NanoVHF/Meshtastic-DIY/Antennas/3...8 el PCB Yagi/3el_870MHz_D4mm_3el_basa.png

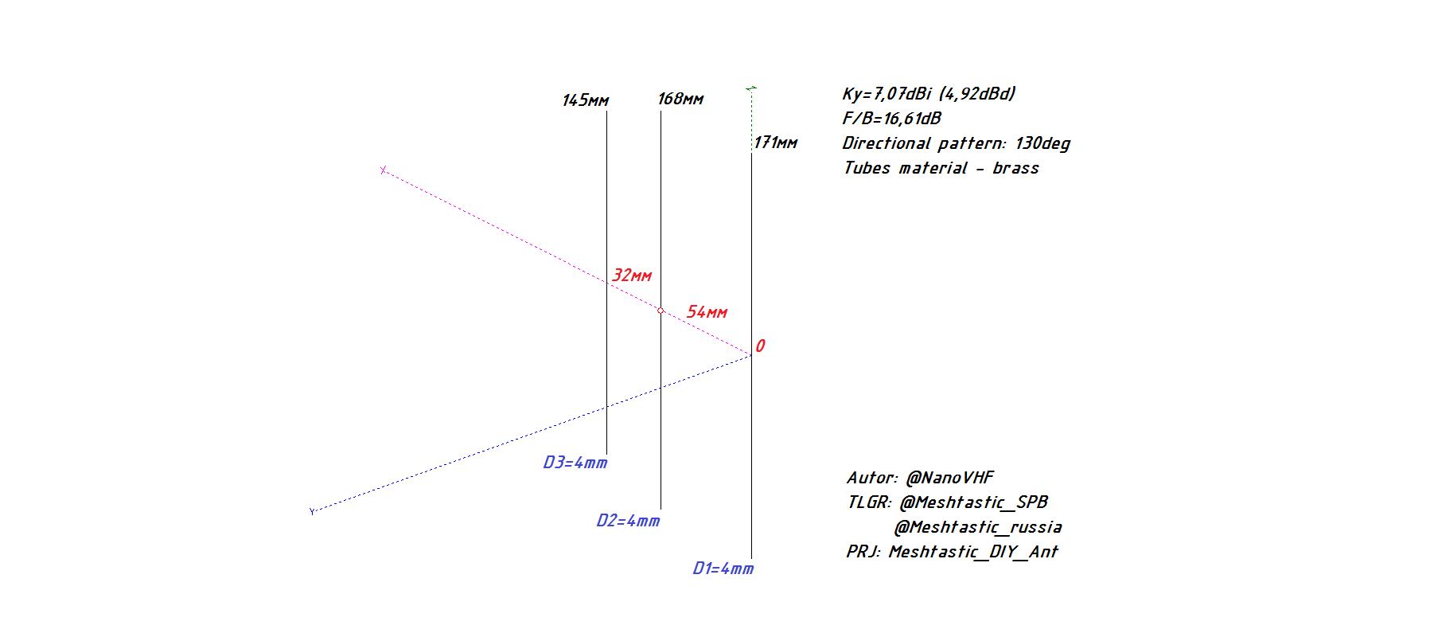
Antennas/3...8 el PCB Yagi/3el_870MHz_D4mm_3el_basa.png
