NanoVHF/Meshtastic-DIY/Antennas/3...8 el PCB Yagi/PCB/870M_3El_Baza_PCB.png

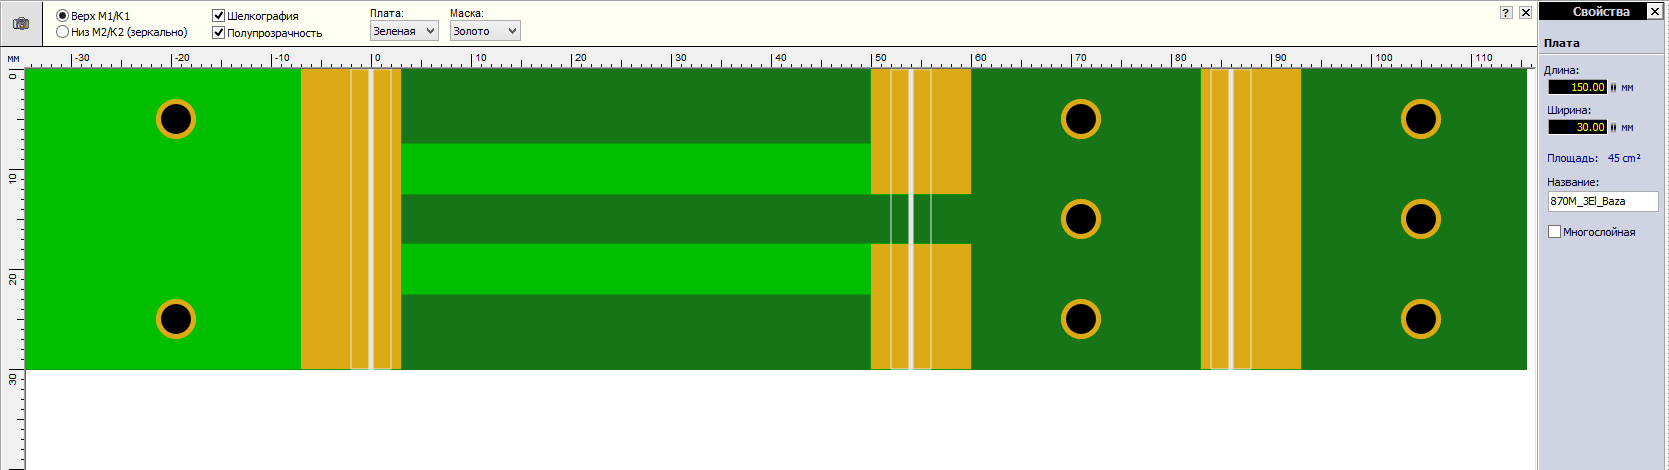
Antennas/3...8 el PCB Yagi/PCB/870M_3El_Baza_PCB.png
