NanoVHF/Meshtastic-DIY/Antennas/3...8 el PCB Yagi/photo_2021-12-09_18-13-56.jpg

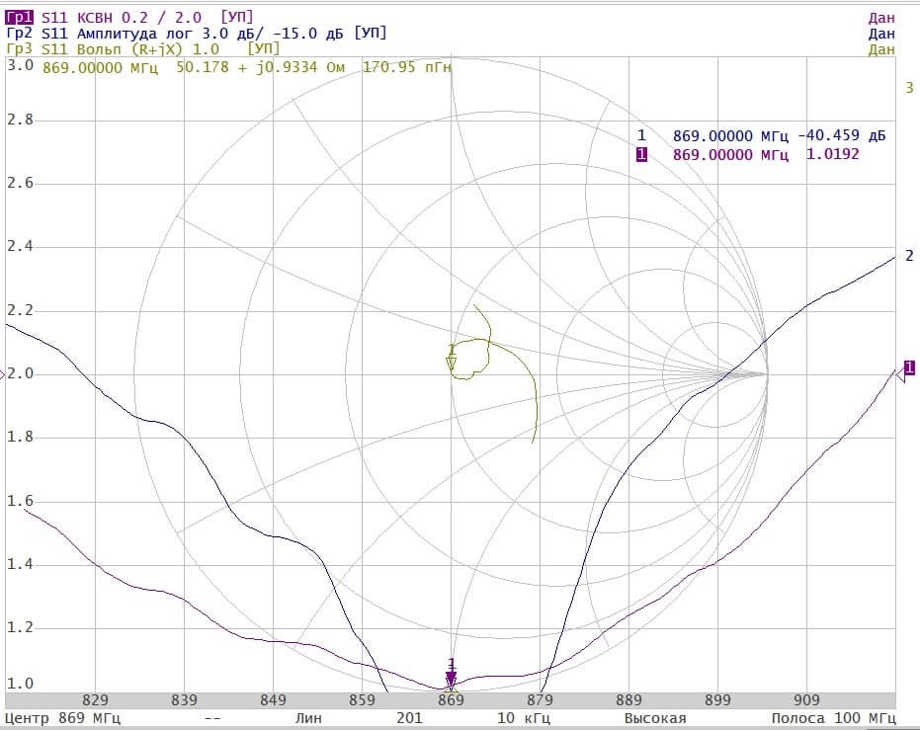
Antennas/3...8 el PCB Yagi/photo_2021-12-09_18-13-56.jpg
