NanoVHF/Meshtastic-DIY/Antennas/3El Yagee/2021-09-16 12_12_45-Планар  CABAN R54 Векторный рефлектометр  85-5400 МГц  v20.4.1.png

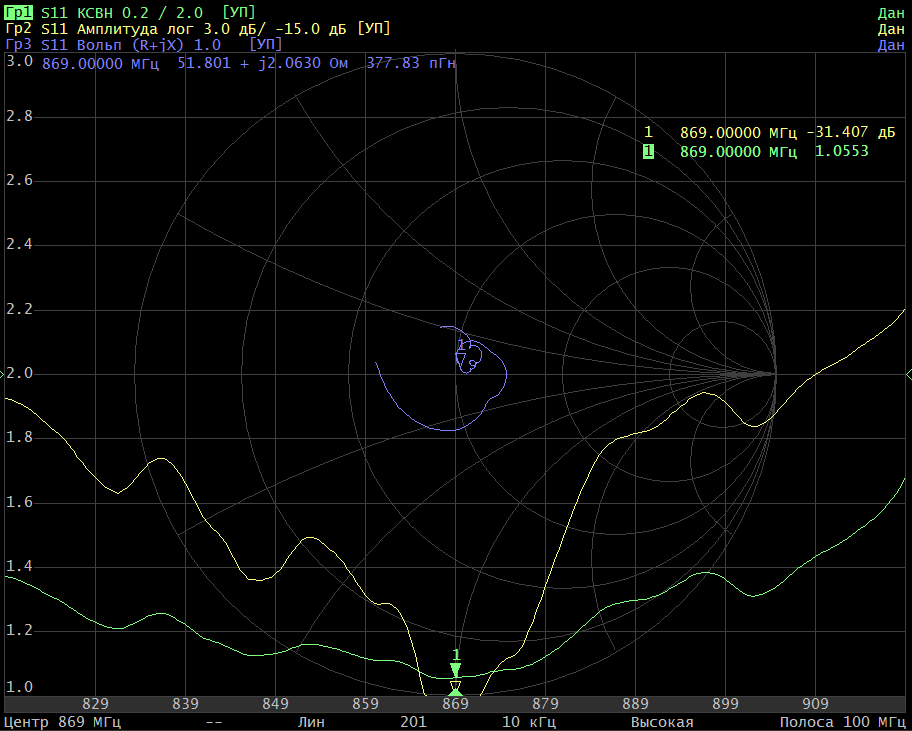
Antennas/3El Yagee/2021-09-16 12_12_45-Планар CABAN R54 Векторный рефлектометр 85-5400 МГц v20.4.1.png
