NanoVHF/Meshtastic-DIY/Antennas/3El Yagee/2021-09-16 12_13_56-MMANA-GAL basic P__ANT-ISM_Yagee_3el_3el_850-880MHz_D4mm_80mm.maa.png

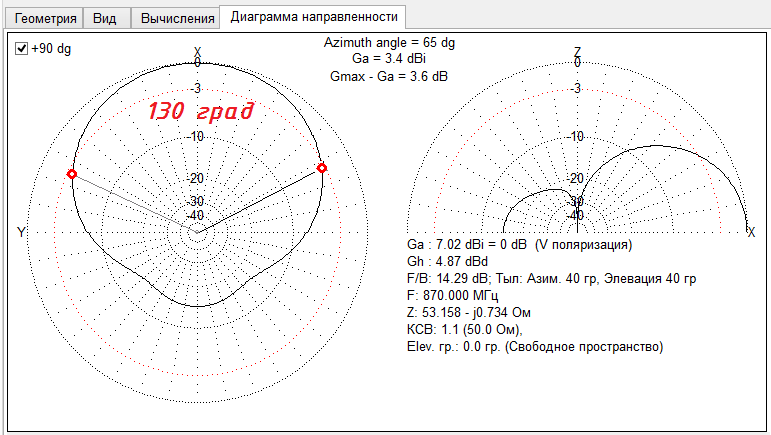
Antennas/3El Yagee/2021-09-16 12_13_56-MMANA-GAL basic P__ANT-ISM_Yagee_3el_3el_850-880MHz_D4mm_80mm.maa.png
