NanoVHF/Meshtastic-DIY/Antennas/3El Yagee/2021-09-16 12_38_03-MMANA-GAL basic  P__ANT-ISM_Yagee_5el_5el_870MHz_D4mm_170x170mm.maa.png

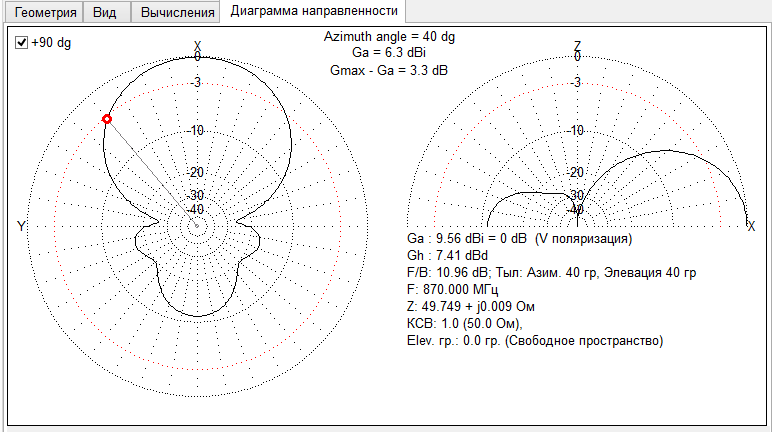
Antennas/3El Yagee/2021-09-16 12_38_03-MMANA-GAL basic P__ANT-ISM_Yagee_5el_5el_870MHz_D4mm_170x170mm.maa.png
