NanoVHF/Meshtastic-DIY/Antennas/3El Yagee/NanoVHF_3el_meshtastic.png

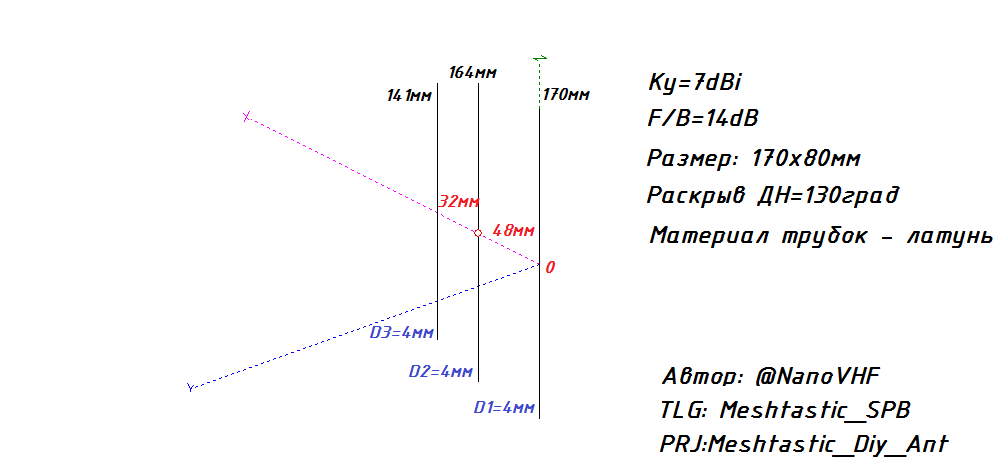
Antennas/3El Yagee/NanoVHF_3el_meshtastic.png
