NanoVHF/Meshtastic-DIY/Antennas/3El Yagee/NanoVHF_3el_meshtastic_869M.png

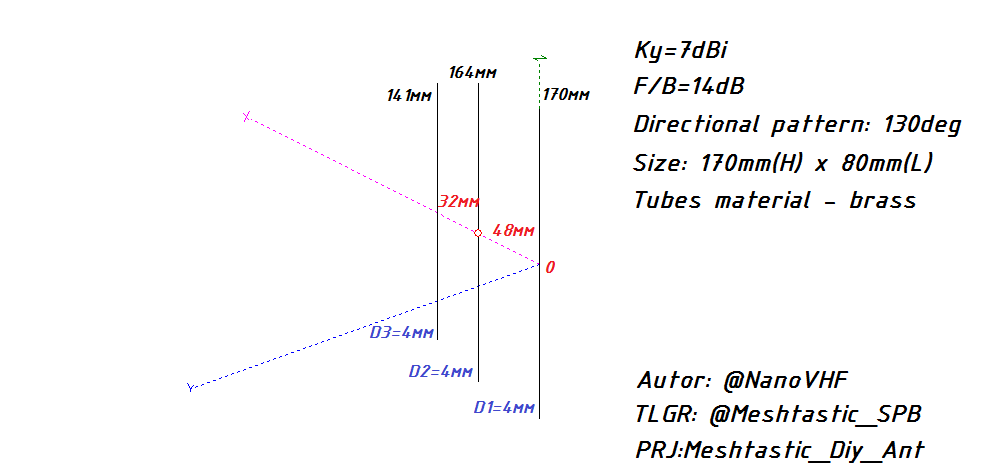
Antennas/3El Yagee/NanoVHF_3el_meshtastic_869M.png
