NanoVHF/Meshtastic-DIY/Antennas/3El Yagee/NanoVHF_3el_meshtastic_eng_1.jpg

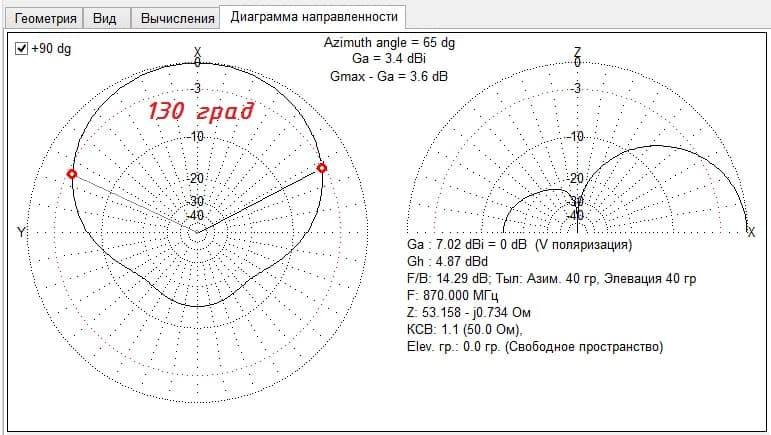
Antennas/3El Yagee/NanoVHF_3el_meshtastic_eng_1.jpg
