NanoVHF/Meshtastic-DIY/PCB/ESP-32-devkit_EBYTE-E22/EBYTE-E22-adapter-board/E22-XXXMXXS_bottom.png

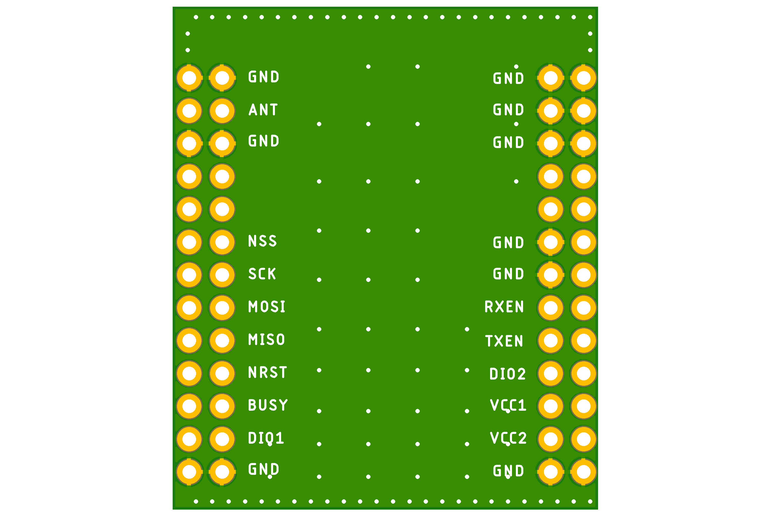
PCB/ESP-32-devkit_EBYTE-E22/EBYTE-E22-adapter-board/E22-XXXMXXS_bottom.png
