NanoVHF/Meshtastic-DIY/PCB/ESP-32-devkit_EBYTE-E22/Mesh-v1.02-2LCD/Meshtastic-DIY_v2_top.png

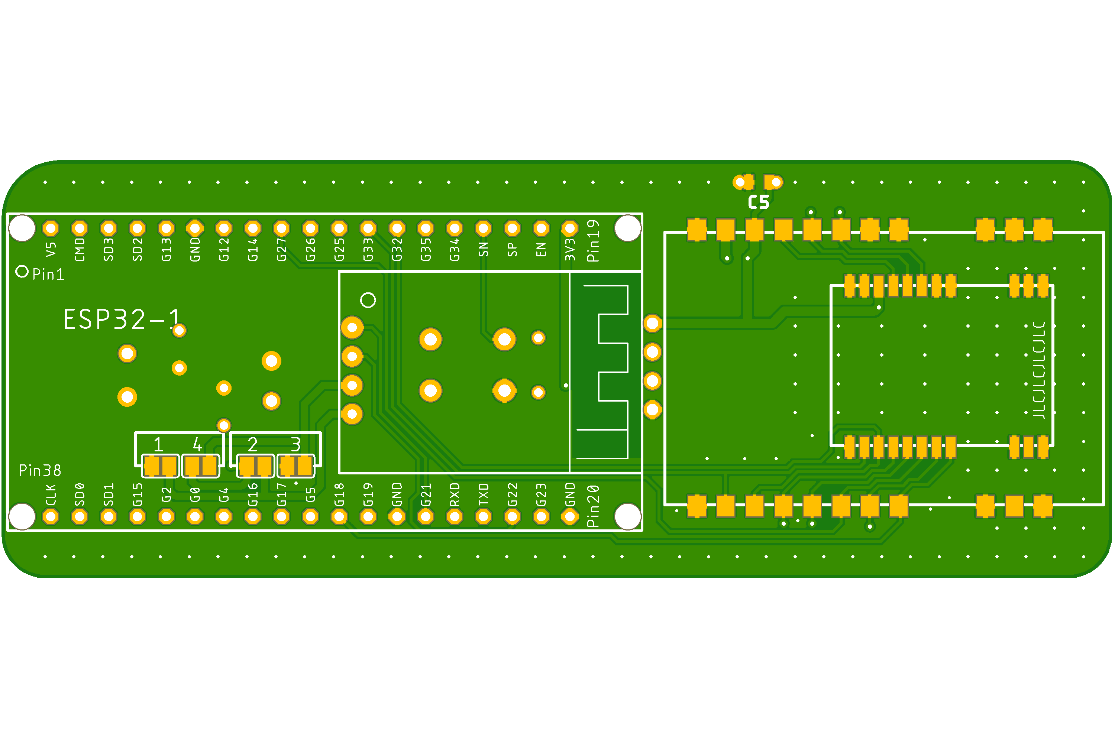
PCB/ESP-32-devkit_EBYTE-E22/Mesh-v1.02-2LCD/Meshtastic-DIY_v2_top.png
