NanoVHF/Meshtastic-DIY/PCB/ESP-32-devkit_EBYTE-E22/Mesh-v1.03-2LCD-FreePins/Meshtastic-DIY_v1.03_top.png

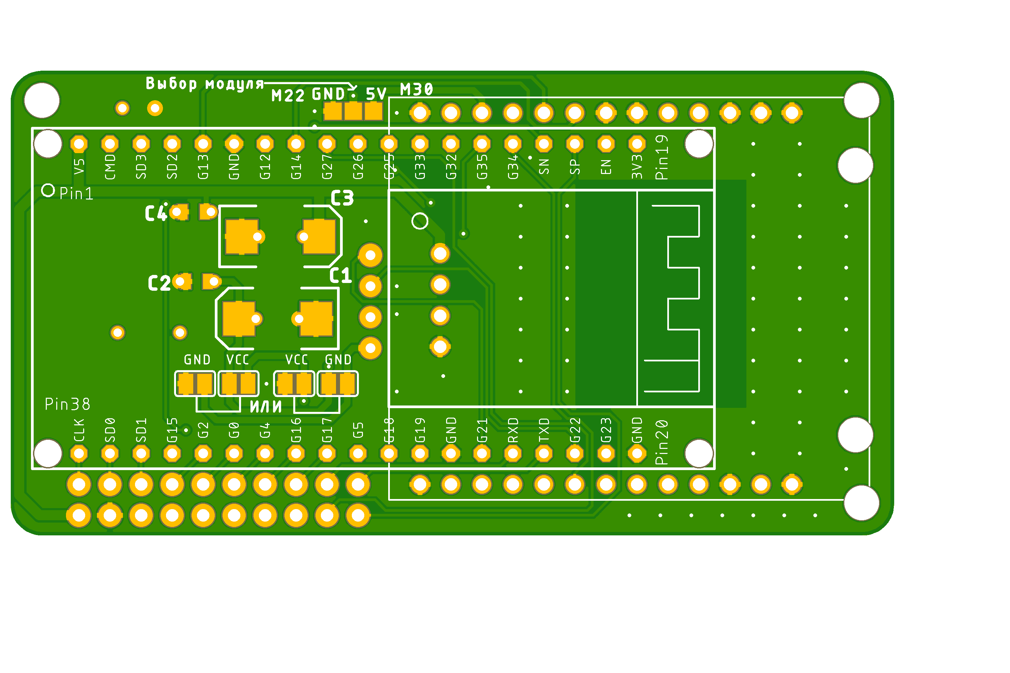
PCB/ESP-32-devkit_EBYTE-E22/Mesh-v1.03-2LCD-FreePins/Meshtastic-DIY_v1.03_top.png
