NanoVHF/Meshtastic-DIY/PCB/ESP-32-devkit_EBYTE-E22/Mesh-v1.04-TTGO-T8/Meshtastic-DIY_v4_TTGO-T8-18_top.png

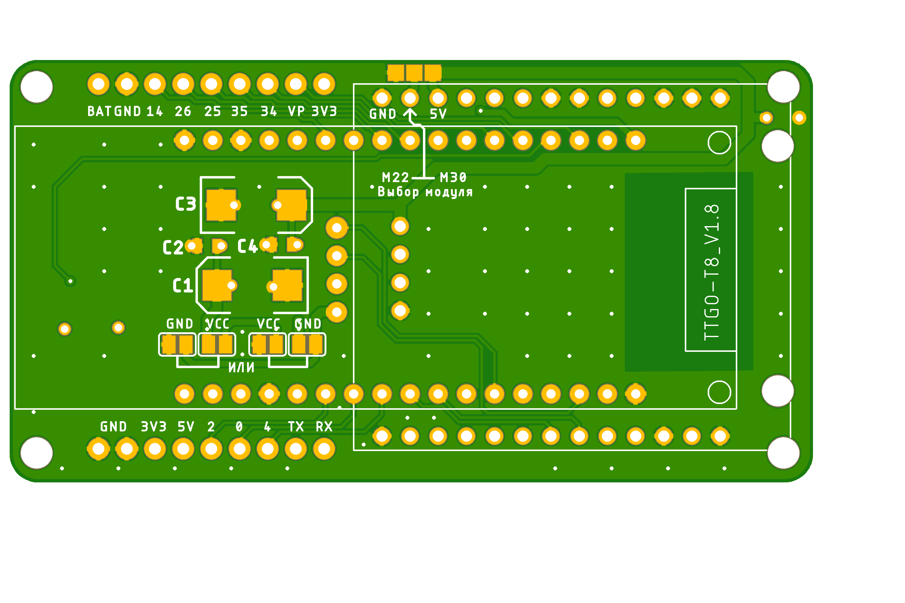
PCB/ESP-32-devkit_EBYTE-E22/Mesh-v1.04-TTGO-T8/Meshtastic-DIY_v4_TTGO-T8-18_top.png
