NanoVHF/Meshtastic-DIY/PCB/ESP-32-devkit_EBYTE-E22/Mesh-v1.04-TTGO-T8/sch.png

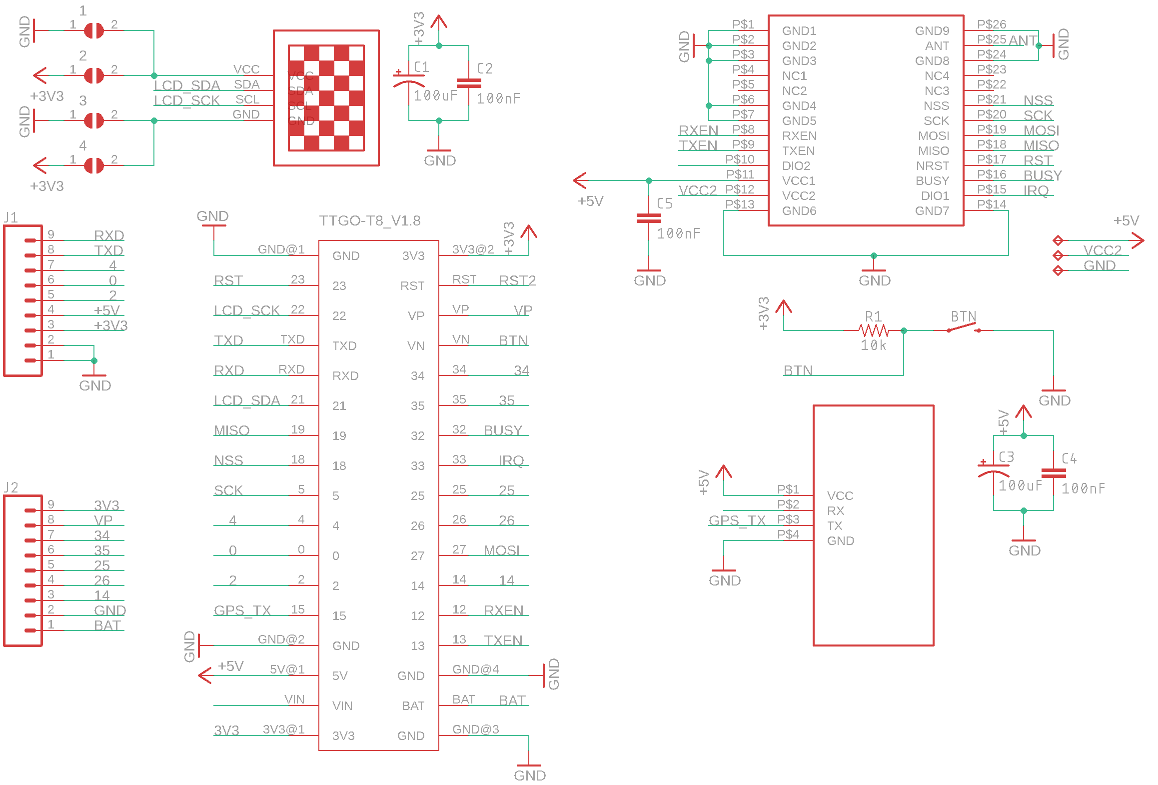
PCB/ESP-32-devkit_EBYTE-E22/Mesh-v1.04-TTGO-T8/sch.png
