NanoVHF/Meshtastic-DIY/PCB/ESP-32-devkit_EBYTE-E22/Mesh-v1.06-TTGO-T18/Meshtastic-DIY_v2.3_TTGO-T18-V30_sch.png

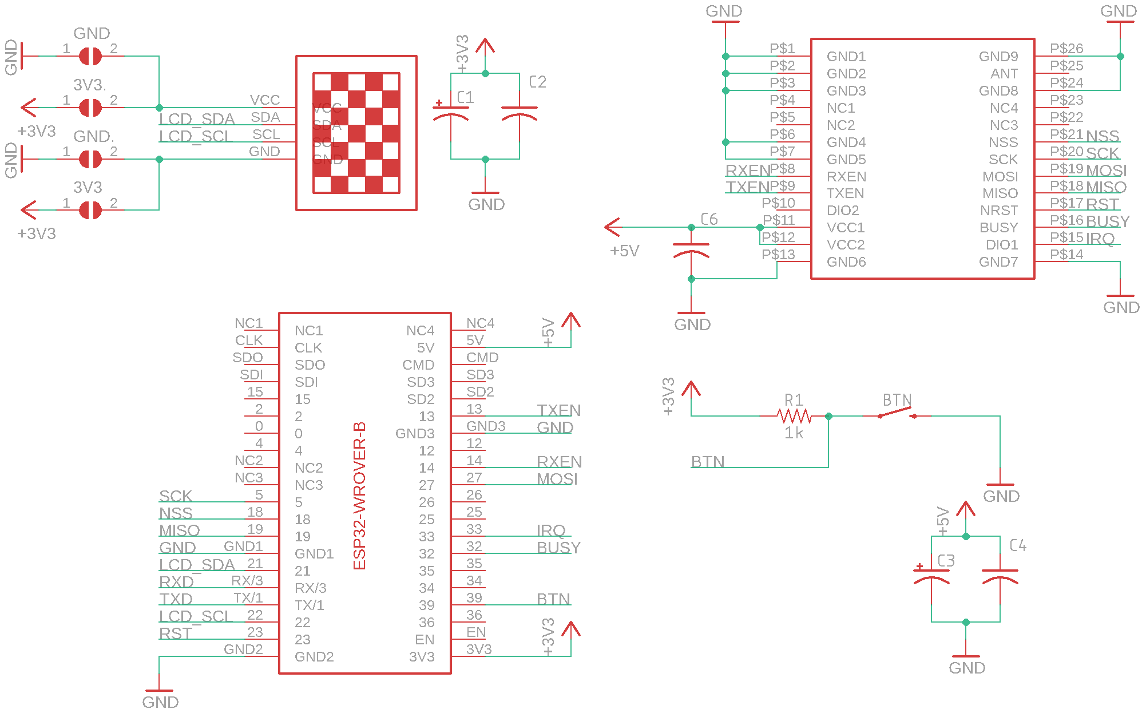
PCB/ESP-32-devkit_EBYTE-E22/Mesh-v1.06-TTGO-T18/Meshtastic-DIY_v2.3_TTGO-T18-V30_sch.png
