NanoVHF/Meshtastic-DIY/PCB/ESP-32-devkit_EBYTE-E22/Mesh-v1.06-TTGO-T18/route.PNG

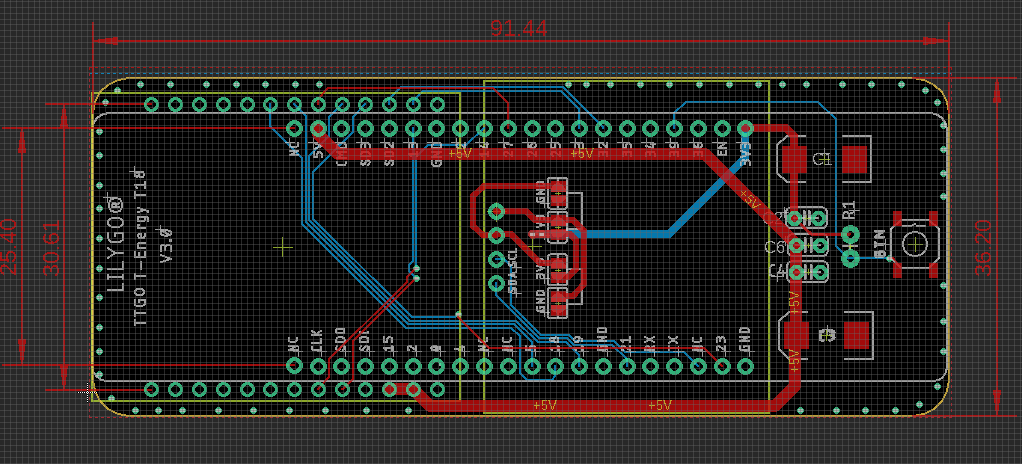
PCB/ESP-32-devkit_EBYTE-E22/Mesh-v1.06-TTGO-T18/route.PNG
