NanoVHF/Meshtastic-DIY/PCB/ESP-32-devkit_EBYTE-E22/Meshtastic-DIY_v1.05/Meshtastic-DIY_v1.05_top.png

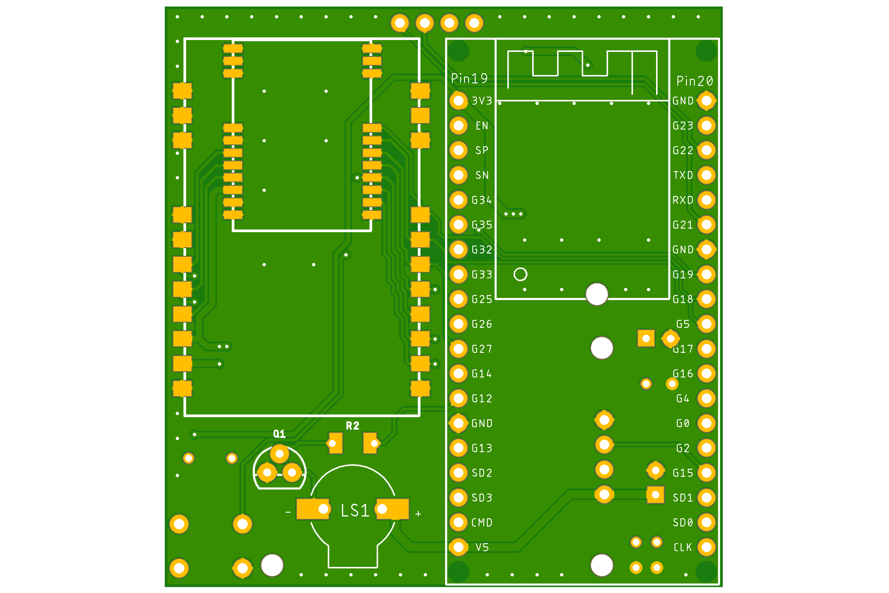
PCB/ESP-32-devkit_EBYTE-E22/Meshtastic-DIY_v1.05/Meshtastic-DIY_v1.05_top.png
